Technologyman00/Teensy-PC_RGB_Controller/RGBController/RGBController/include/functions.h

#ifndef FUNCTIONS_H
#define FUNCTIONS_H

#include <stdint.h>
#include "Arduino.h"
#include <SD.h>
#include <SPI.h>
#include <math.h>
#include "global.h"

void smartDelay(int delayMS);
void HSVtoRGB(unsigned int H_bytes, byte S_byte, byte V_byte);

void CreateLedDevice(int portForDevice, int pixelsInDevice);
int GetLEDStart(int port);

void getSerialUpdates();
void charArrayWriter(char *arrayToBeWritten, char *arrayFrom);

void softRestart();
void initalizeLEDCommands();

void createStartupFile();
void createStartupFile(char* fileName);

void createDefaultFile();


#endif  // FUNCTIONS_H
