Technologyman00/Teensy-PC_RGB_Controller/1 Tools/WriteFileOverSerialTest/SendFile.py

import serial
import time

f = serial.Serial('COM4', '9600')

print("Sending File...")

f.write(b'w frames2000')

time.sleep(2)

f.write((7656).to_bytes(4, byteorder='big'))

time.sleep(1)

f.write((4).to_bytes(1, byteorder='big')) # First Frame

f.write((3).to_bytes(1, byteorder='big')) # Create Device
f.write((1).to_bytes(1, byteorder='big')) # Port
f.write((9).to_bytes(1, byteorder='big')) # Number of LEDS

f.write((2).to_bytes(1, byteorder='big'))
f.write((10).to_bytes(2, byteorder='big'))

for ii in range(0, 255):
        print((ii/255)*100)
        time.sleep(0.1)
        f.write((1).to_bytes(1, byteorder='big'))
        f.write((1).to_bytes(1, byteorder='big'))
        for i in range(0, 9): # First Frame all White
                f.write((ii).to_bytes(1, byteorder='big'))
                f.write((255).to_bytes(1, byteorder='big'))
                f.write((255).to_bytes(1, byteorder='big'))

        f.write((4).to_bytes(1, byteorder='big')) # Start Second Frame
